knurtz/EmergencyWake/BrassPlates/BrassPlateDisplay_PlaquesOnly.png

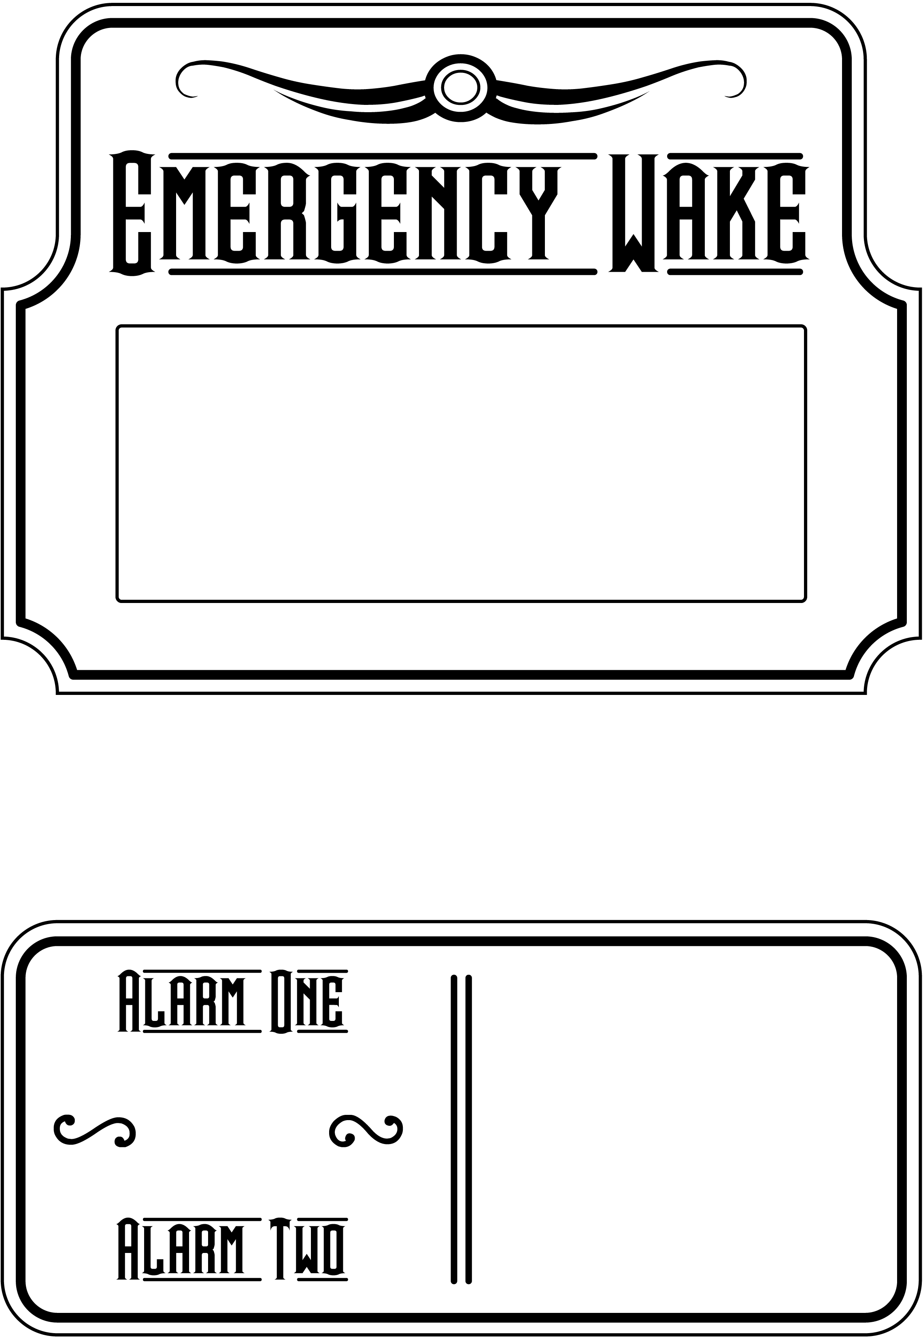
BrassPlates/BrassPlateDisplay_PlaquesOnly.png
