knurtz/EmergencyWake/Board/AssemblyInformation/DFM Analysis/00_DFM_Analysis03.png

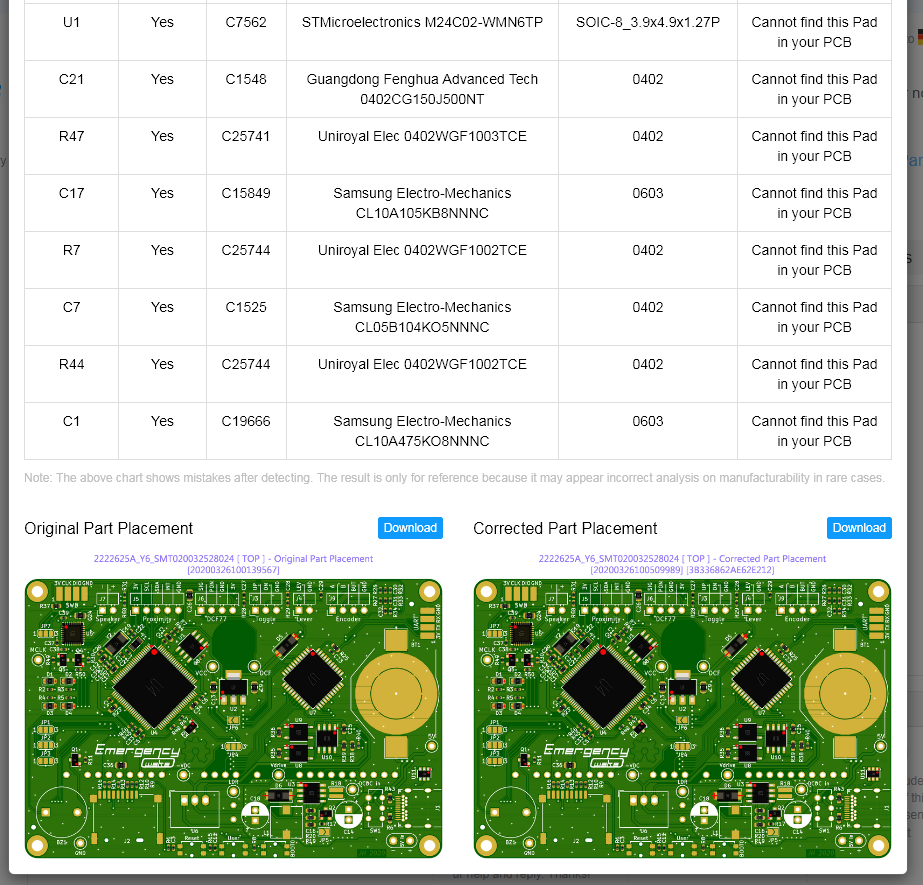
Board/AssemblyInformation/DFM Analysis/00_DFM_Analysis03.png
