knurtz/EmergencyWake/Board/AssemblyInformation/DFM Analysis/01_Original_Placement_Produce_DanZhi.SMT_Original_Snapshot.Top.2222625A_Y6.SMT020032528024.png

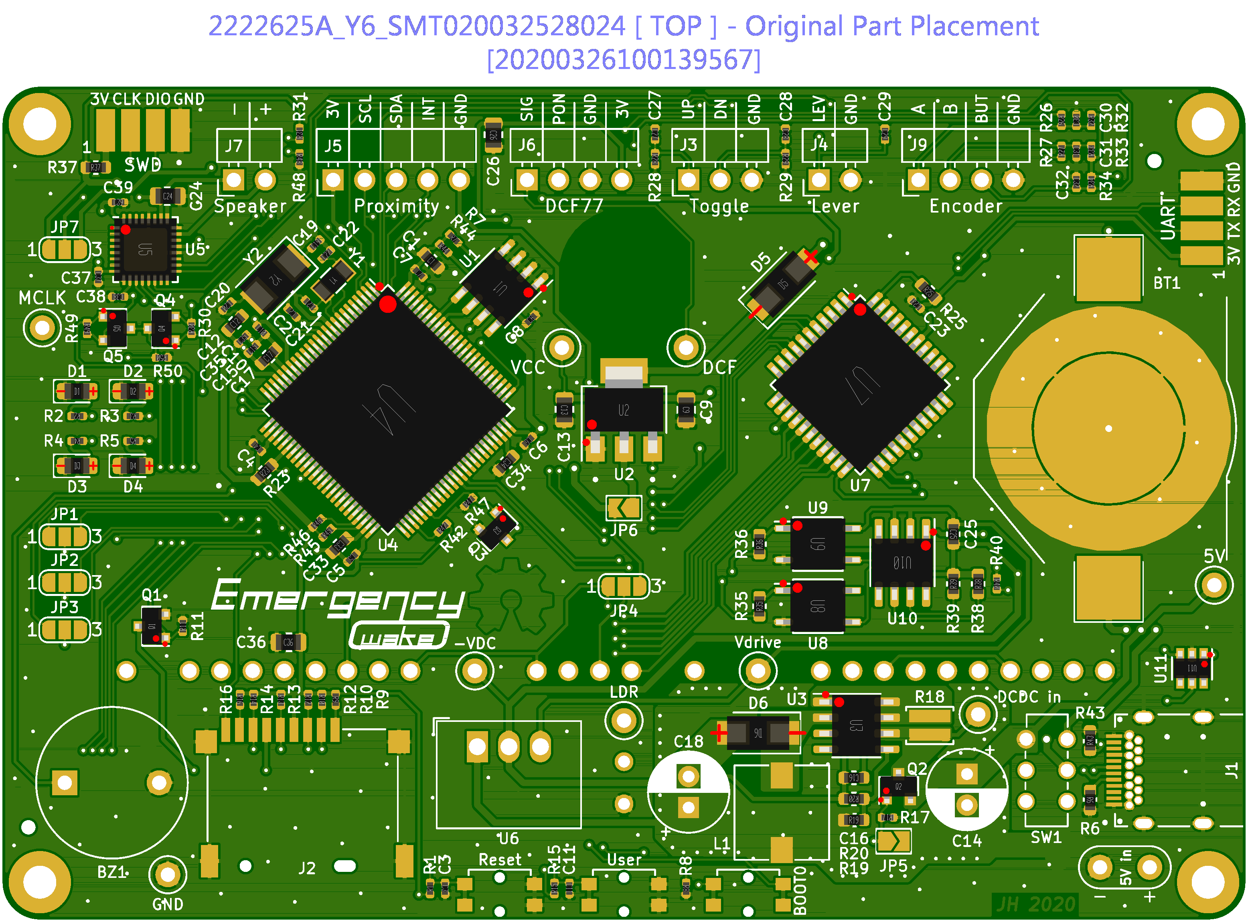
Board/AssemblyInformation/DFM Analysis/01_Original_Placement_Produce_DanZhi.SMT_Original_Snapshot.Top.2222625A_Y6.SMT020032528024.png
