knurtz/EmergencyWake/Code/inc/wave_header.h

#ifndef WAVE_HEADER_H
#define WAVE_HEADER_H

#include "ch.h"

typedef struct _chunk
{
	uint32_t    id;             
	uint32_t    size;
 } chunk;

typedef struct _RIFFHeader
{
	 chunk       descriptor;    // "RIFF"
	 uint32_t    type;          // "WAVE"
} RIFFHeader;

typedef struct _WAVEHeader
{
     chunk       descriptor;    // "fmt "
     uint16_t    audioFormat;	// 1 - PCM
     uint16_t    numChannels;	// 1 - mono, 2 - stereo
     uint32_t    sampleRate;
     uint32_t    byteRate;		// byteRate = SampleRate * BlockAlign
     uint16_t    blockAlign;	// BlockAlign = bitsPerSample / 8 * NumChannels
     uint16_t    bitsPerSample;
} WAVEHeader;

typedef struct _FILEHeader
{
    RIFFHeader  riff;
    WAVEHeader  wave;
} FILEHeader;

typedef struct _DATAHeader
{
	chunk       descriptor;     // "data"
} DATAHeader;

#endif /* WAVE_HEADER_H */
